kesternucum/ECE-Capstone-Team3/Documentation/Poster/Poster Template/poster.pdf

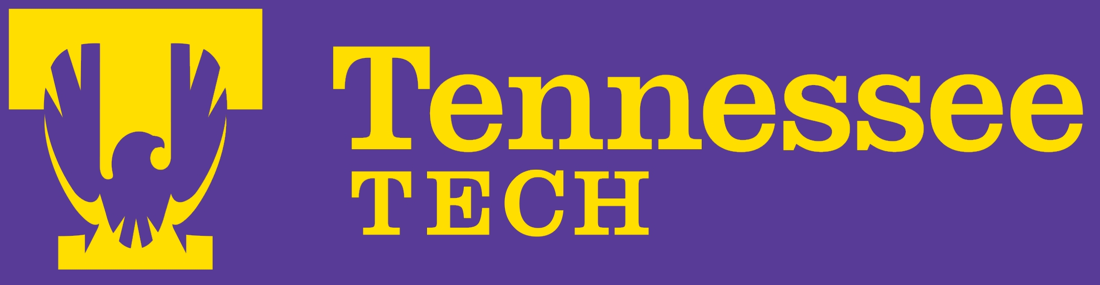
[picture p27: figure]

# Biologically Extending the Gen 2 Artificial Neural Network

## Jesse Roberts

## 1 Dr. Douglas Talbert

2

1Vanderbilt University

| 2Tennessee Technological University

## Biological Neurons

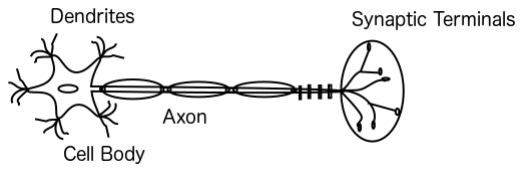
[picture p28: figure]

Figure 1. Neuron Diagram

Dendrites provide the input field to the neuron
The voltage difference from cell body to the exterior of the cell controls acon potenal The axon carries the acon potenal to other locaons in the network
Synapc terminals transmit the acon potenal from the axon to other neural dendrites

With the arrival of each acon potenal at a synapc terminal, neurotransmiers are released and carried into the neuron by way of ion channels and pumps. The ions change the voltage present across the membrane of the cell body. If the membrane voltage increases past the acon potenal threshold, an acon potenal will occur and propagate along the axon to the synapc terminals. A membrane voltage that has been elevated is referred to as depolarized. In homeostasis a neuron aempts to enforce polarizaon, remaining ready to receive input leading to an acon potenal.

raction = −rpol +

∑α ∗ rdepol, | α ≥ 0 | (1)

firing rate of the target neuron is dependent upon the rate of depolarizaon
rpol is the internal rate of polarizaon
rdepol is the rate at which a specific synapse is firing
α is the amount of neurotransmier released with each pulse at the synapc terminal raction is the rate of acon potenal propagated along the axon
Summaon accounts for mulple synapses

## Biological Interneurons

Interneurons provide external polarizaon to the biological neural network. Eq 1 is modified to reflect external polarizaon in 2.

raction = −rpol +

∑α ∗ βInter ∗ rdepol, | 0 ≤ β ≤ 1 α ≥ 0 | (2)

Interneurons allow for selecve gang of inputs to different regions of the dendrite Interneurons facilitate dynamic changes in the relave contribuon of inputs βInter accounts for the gang associated with a parcular synapc connecon

*Neither Eq 1 or 2 is intended to be complete characterizaons of a neuron. Rather both should be understood to capture the relevant pieces of neural acvity necessary to develop Gen 1 and 2 neural networks.

## Artificial Neurons

Gen 1 ANNs are considered those limited to classificaon. They are incapable of performing regression because the output assumes only the values one or zero. The perceptron is such a model. This model characterizes neurons as switches as shown in Eq 3.

net =

{
0 b +

∑wj ∗ Ij ≥ 0

1 b +

∑wj ∗ Ij < 0

(3)

wj represents the relave amount of neurotransmiers released or, α in Eq 1

Ij

is the firing rate present at the j

th
synapse
b is the bias associated with this neuron or, rpol

in Eq 1

Gen 2 ANNs are where the bulk of research in computer science has been focused. The ability to output a connuous value from zero to one provided the ability to learn non-linear regressive approximaons thanks to connuously differenable acvaon funcons. The typical equaon for a Gen 2 ANN is presented in Eq 4. The step funcon has been replaced by the sigmoid funcon represented by σ.

net = σ

(
b +

∑wj ∗ Ij

)
(4)

## Artificial Interneurons (INNs)

Contribuon

Extended the Gen 2 ANN model to include interneurons
Facilitated selecvely gang the input along any edge to edge connecon between neurons Derived the backpropagaon equaons necessary for an arbitrary INN
Outperformed the base ANN when applied to the MNIST dataset

INN Model Requirements

Given a set I of inputs to neuron n it is required that any I

′ ∈ I be modifiable such that the set I

′∆I is le[ unchanged. This lends itself to the addion of some weight β to the ANN equaon. β must be variable depending on the inputs presented to the ANN.

INN Model

Figure 2. Neuron Diagram

net = σ

(
b +

∑wj ∗ βj ∗ Ij

)
(5)

βj = σ

(
b

′ +

∑w
′
j ∗ I

′
j

)
(6)

*It should be understood that the point of this paper is not to build a beer performing ANN. It is the beginning of invesgaon towards a new more biologically plausible model.

## Results: Applying an INN to MNIST

Experimental Setup

MNIST is a well known problem in machine learning
MNIST Consists of 60000 training images of handwrien digits and 10000 test images
The experiment proves the model learns and converges to a soluon in a mul-output, large input environment
The INN model was implemented in Tensorflow
Interneurons were only applied to the hidden layer
All other values for the interneuron ANN were the same as the principal cell ANN The principal cell ANN and interneuron ANN were opmized simultaneously using backpropogaon

Experimental Results

The INN outperformed the ANN
The performance of the ANN as applied to the test set was 96.9
The performance of the INN was 97.2
The model has been shown to converge and perform beer than the naive case The INN did not outperform the ANN more most likely due to the problem domain The power fo the INN is believed to be the abilit to dynamically contextualize

## Future Work

Neuroscience

Neuroscience has not been able to make a definive asseron about interneuron input feature selecon, we intend to provide an answer using this model. We have chosen a Gen 2 framework because more is computaonally known in this domain. The hope is that through the isolaon of variables an answer will be approximated.

Mul-Task and Transfer Learning

The literature review was rich with similar work in mul-task learning. It is hoped that by training the principal ANN weights with unity interneuron ANN weights, the special case of INN backpropagaon, the principal cell ANN will converge to task 1 and allow the interneuron ANN to learn task differenaon. A similar idea can be applied to experiment with transfer learning.

## References

[1] J. V. Arthur and K. A. Boahen.
Synchrony in silicon: The gamma rhythm.
IEEE Transacࢼons on Neural Networks, 18(6):1815–1825, 2007.
[2] T. Freund and S. Kali.
Interneurons.
Scholarpedia, 3(9):4720, 2008.
[3] J. Kirkpatrick, R. Pascanu, N. Rabinowitz, J. Veness, G. Desjardins, A. A. Rusu,
K. Milan, J. Quan, T. Ramalho, A. Grabska-Barwinska, et al.
Overcoming catastrophic forgeng in neural networks.
Proceedings of the naࢼonal academy of sciences, page 201611835, 2017.
[4] D. Purves, G. Augusne, D. Fitzpatrick, W. Hall, A. M. Lamana, and W. JO.
Sm (2004) neuroscience, 2004.
[5] A. Schuster and D. Berrar.
Towards nature-inspired modularizaon of arficial neural networks via stac and dynamic weights.
In Biomedical Informaࢼcs and Technology, pages 219–234. Springer, 2014.
[6] L. Wan, M. Zeiler, S. Zhang, Y. Le Cun, and R. Fergus.
Regularizaon of neural networks using dropconnect.
In Internaࢼonal Conference on Machine Learning, pages 1058–1066, 2013.
