kesternucum/ECE-Capstone-Team3/Documentation/Images/12_Volts.PNG

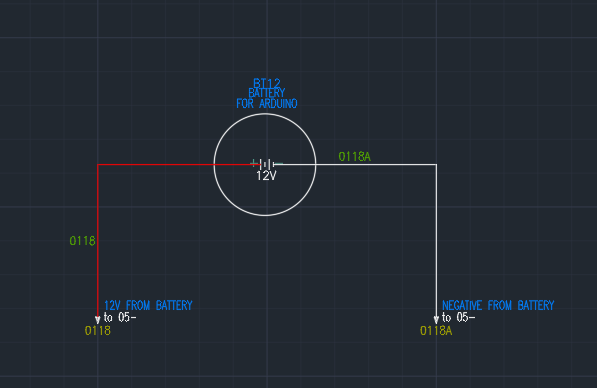
Documentation/Images/12_Volts.PNG
