kesternucum/ECE-Capstone-Team3/Documentation/Images/Arduino_Uno_Autocad.PNG

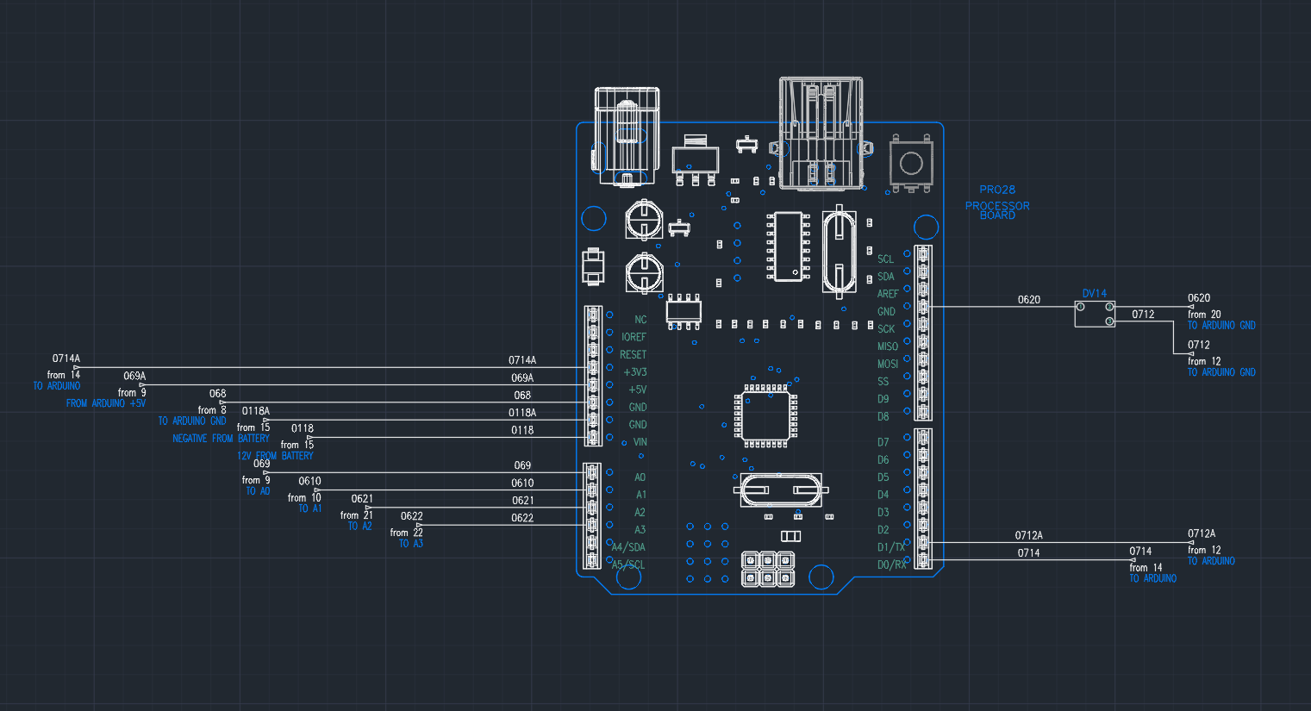
Documentation/Images/Arduino_Uno_Autocad.PNG
