kesternucum/ECE-Capstone-Team3/Documentation/Images/Backpanel.PNG

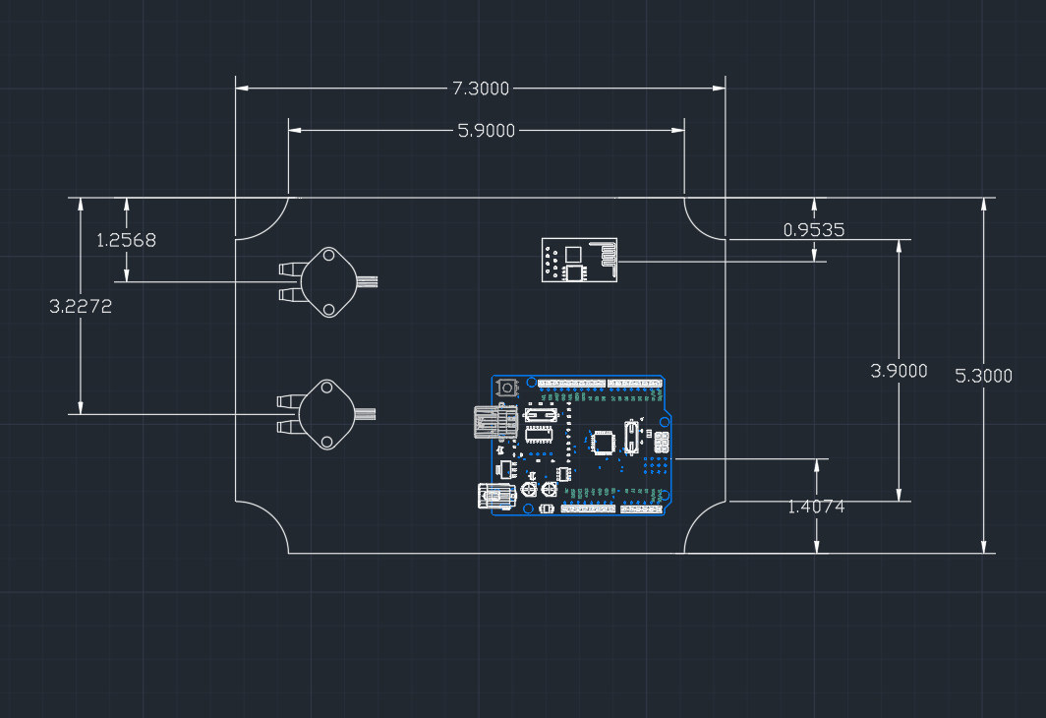
Documentation/Images/Backpanel.PNG
