kesternucum/ECE-Capstone-Team3/Documentation/Images/Dif_Pressure_Sensor.PNG

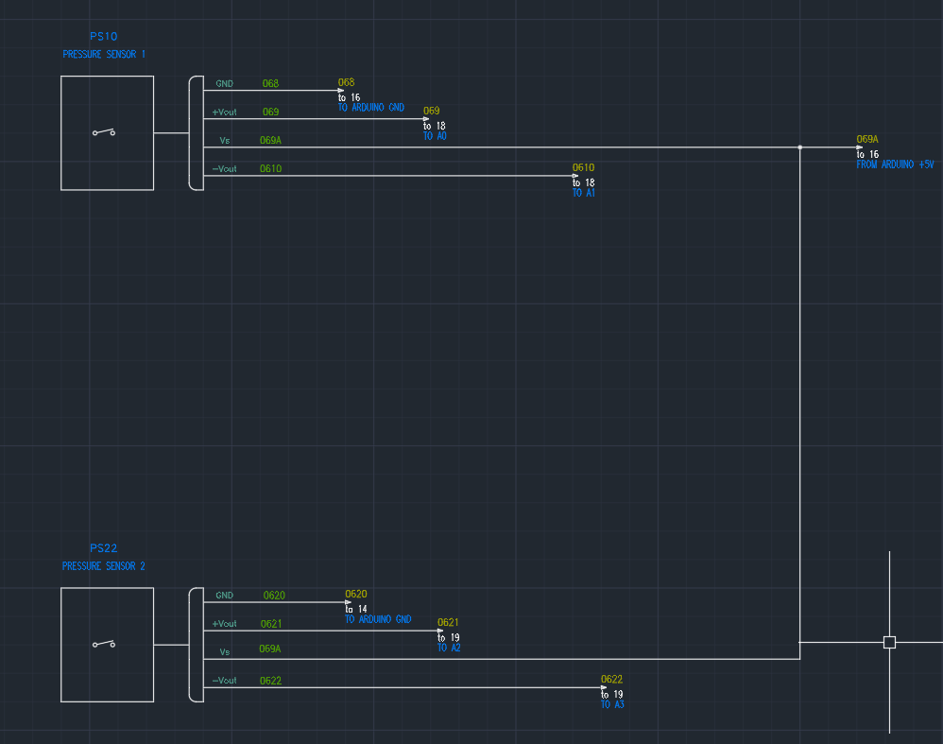
Documentation/Images/Dif_Pressure_Sensor.PNG
