kesternucum/ECE-Capstone-Team3/Documentation/Images/Wireless_Com_Board.PNG

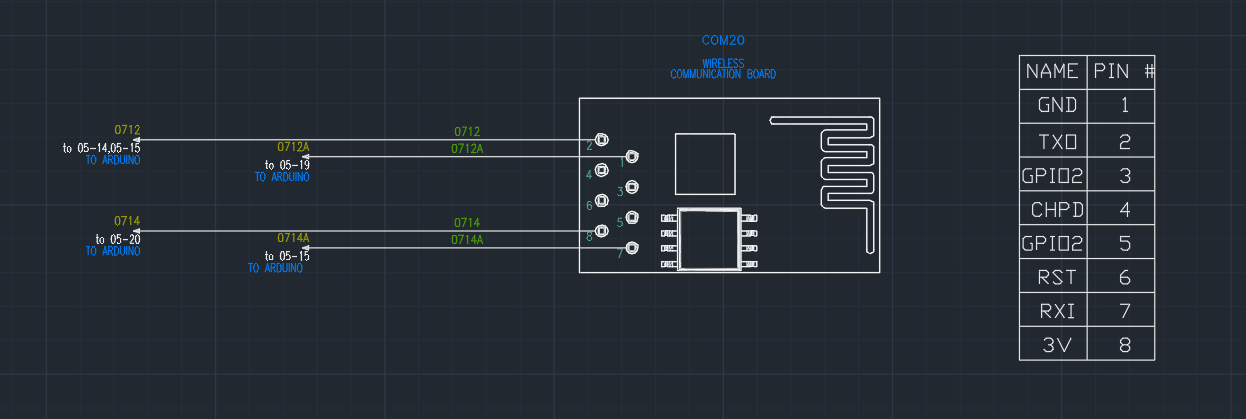
Documentation/Images/Wireless_Com_Board.PNG
